JeremyJStarcher/retro-keys/keyboards/c64-vic20/imgs/c64-keyboard-stickers.png

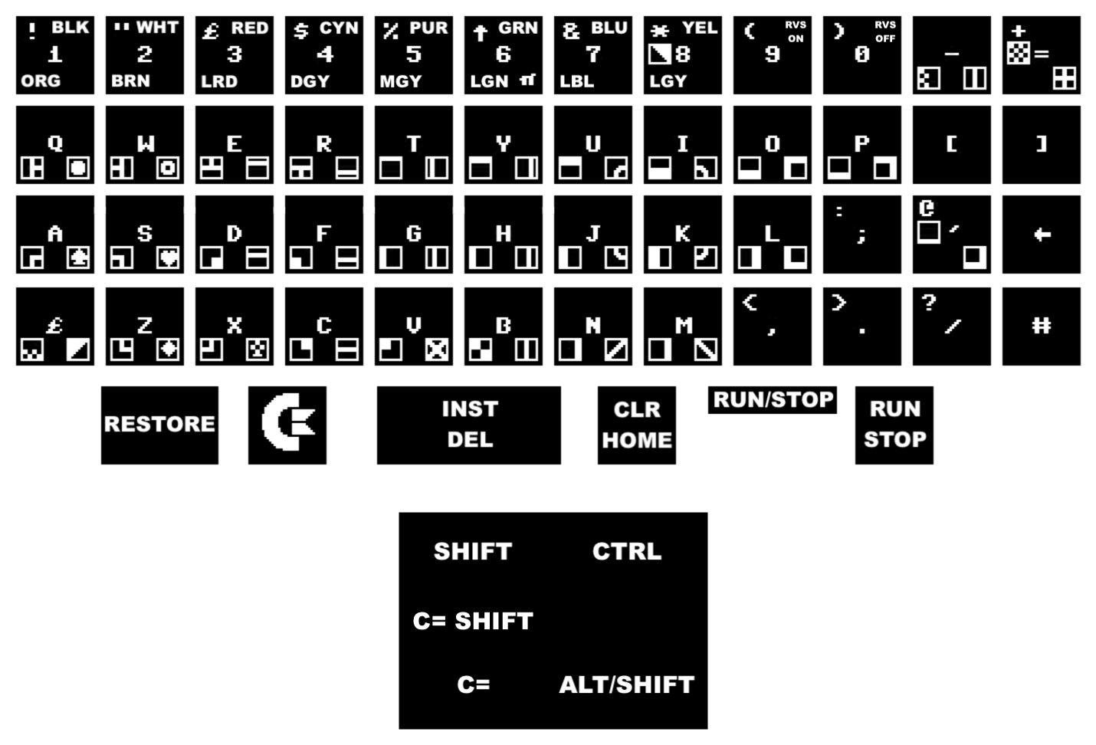
keyboards/c64-vic20/imgs/c64-keyboard-stickers.png
