JeremyJStarcher/retro-keys/keyboards/openscad/puzzlecut/images/OctopusThickLegs.png

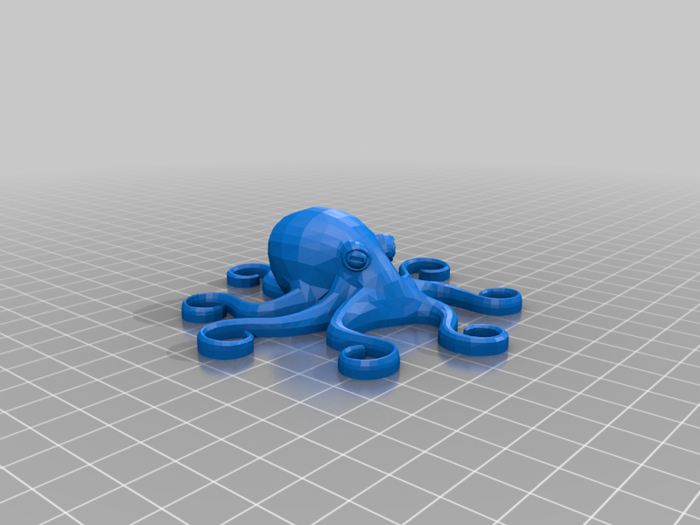
keyboards/openscad/puzzlecut/images/OctopusThickLegs.png
