JeremyJStarcher/retro-keys/keyboards/kicad-lib/3d-models/SOD-diodes/SOD-923 0.3mm Lead Width.step

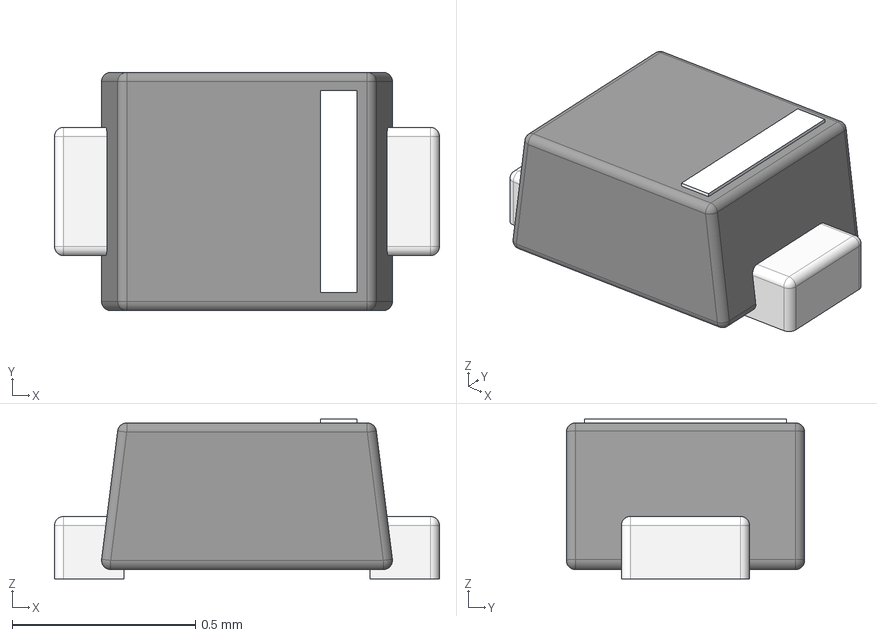
[picture p33: CAD file, 2022-12-26]
keyboards/kicad-lib/3d-models/SOD-diodes/SOD-923 0.3mm Lead Width.step
1.05 x 0.65 x 0.435 mm
