JeremyJStarcher/retro-keys/keyboards/atari-a8/case/case-position.scad

include <../../openscad/utils.scad>;
BASE_THICKNESS = 4;
BOARD_X1 = -216.81315;
BOARD_Y1 = 236.4081;
BOARD_X2 = 138.94315;
BOARD_Y2 = 377.8519;
BOARD_LEN = 355.7563;
BOARD_WIDTH = 141.44379999999998;
CASE_HEIGHT = 10;
STANDOFF_HOLE_INNER_DIAMETER = 4.4;
STANDOFF_HOLE_OUTER_DIAMETER = 6;
STANDOFF_HOLE_HEIGHT = 5;
MOUNTING_HOLE_D = 3.2;
MOUNTING_HOLE_OFFSET = 5;
keyStandoffs = [
[48.935050000000004,-203.38],
[72.7475,-203.38],
[91.7975,-203.38],
[110.8475,-203.38],
[129.8975,-203.38],
[148.9475,-203.38],
[167.9975,-203.38],
[187.0475,-203.38],
[206.0975,-203.38],
[225.1475,-203.38],
[244.1975,-203.38],
[263.2475,-203.38],
[282.2975,-203.38],
[301.3475,-203.38],
[320.3975,-260.53000000000003],
[301.3475,-279.58],
[320.3975,-279.58],
[339.4475,-279.58],
[48.935050000000004,-222.43],
[82.27250000000001,-222.43],
[101.3225,-222.43],
[120.3725,-222.43],
[139.4225,-222.43],
[158.4725,-222.43],
[177.5225,-222.43],
[196.5725,-222.43],
[215.6225,-222.43],
[234.6725,-222.43],
[253.72250000000003,-222.43],
[272.7725,-222.43],
[291.8225,-222.43],
[314.8725,-229.43],
[365.6413,-177.1862],
[365.6413,-205.7612],
[365.6413,-229.5737],
[365.6413,-253.38620000000003],
[48.935,-241.48000000000002],
[87.035,-241.48000000000002],
[106.08500000000001,-241.48000000000002],
[125.13499999999999,-241.48000000000002],
[144.185,-241.48000000000002],
[163.235,-241.48000000000002],
[182.285,-241.48000000000002],
[201.335,-241.48000000000002],
[220.385,-241.48000000000002],
[239.435,-241.48000000000002],
[258.485,-241.48000000000002],
[277.535,-241.48000000000002],
[296.585,-241.48000000000002],
[315.63505,-241.48000000000002],
[365.6413,-277.19870000000003],
[113.2288,-177.1862],
[151.3288,-177.1862],
[175.1413,-177.1862],
[79.89125,-279.58],
[53.69755000000001,-265.53000000000003],
[96.56,-260.53000000000003],
[115.61,-260.53000000000003],
[134.66,-260.53000000000003],
[153.71,-260.53000000000003],
[172.76,-260.53000000000003],
[191.81,-260.53000000000003],
[210.86,-260.53000000000003],
[229.91,-260.53000000000003],
[248.95999999999998,-260.53000000000003],
[268.01,-260.53000000000003],
[287.06005,-260.53000000000003],
[294.2038,-177.1862],
[318.0163,-177.1862],
[139.42255,-279.58],
];
keyBoundingBoxes = [
["ESC", 48.935050000000004, -201.88, 72.74755, -220.92999999999998],
["1", 72.7475, -201.88, 91.7975, -220.92999999999998],
["2", 91.7975, -201.88, 110.8475, -220.92999999999998],
["3", 110.8475, -201.88, 129.8975, -220.92999999999998],
["4", 129.8975, -201.88, 148.94750000000002, -220.92999999999998],
["5", 148.9475, -201.88, 167.9975, -220.92999999999998],
["6", 167.9975, -201.88, 187.0475, -220.92999999999998],
["7", 187.0475, -201.88, 206.09750000000003, -220.92999999999998],
["8", 206.0975, -201.88, 225.1475, -220.92999999999998],
["9", 225.1475, -201.88, 244.19750000000002, -220.92999999999998],
["0", 244.1975, -201.88, 263.2475, -220.92999999999998],
["LT", 263.2475, -201.88, 282.2975, -220.92999999999998],
["GT", 282.2975, -201.88, 301.3475, -220.92999999999998],
["BS", 301.3475, -201.88, 339.4475, -220.92999999999998],
["C_UP", 320.3975, -259.03000000000003, 339.4475, -278.08000000000004],
["C_LEFT", 301.3475, -278.08, 320.39750000000004, -297.13],
["C_DOWN", 320.3975, -278.08, 339.4475, -297.13],
["C_RIGHT", 339.4475, -278.08, 358.4975, -297.13],
["TAB", 48.935050000000004, -220.93, 82.27255, -239.98],
["Q", 82.27250000000001, -220.93, 101.3225, -239.98],
["W", 101.3225, -220.93, 120.3725, -239.98],
["E", 120.3725, -220.93, 139.4225, -239.98],
["R", 139.4225, -220.93, 158.47250000000003, -239.98],
["T", 158.4725, -220.93, 177.5225, -239.98],
["Y", 177.5225, -220.93, 196.57250000000002, -239.98],
["U", 196.5725, -220.93, 215.6225, -239.98],
["I", 215.6225, -220.93, 234.6725, -239.98],
["O", 234.6725, -220.93, 253.72250000000003, -239.98],
["P", 253.72250000000003, -220.93, 272.77250000000004, -239.98],
["DASH", 272.7725, -220.93, 291.8225, -239.98],
["EQUAL", 291.8225, -220.93, 310.8725, -239.98],
["RETURN", 310.8725, -220.93, 339.4475, -239.98],
["HELP", 365.6413, -175.6862, 384.6913, -194.7362],
["RESET", 365.6413, -204.2612, 384.6913, -223.31119999999999],
["OPTION", 365.6413, -228.0737, 384.6913, -247.12369999999999],
["SELECT", 365.6413, -251.88620000000003, 384.6913, -270.93620000000004],
["CONTROL", 48.935, -239.98000000000002, 87.03500000000001, -259.03000000000003],
["A", 87.035, -239.98000000000002, 106.085, -259.03000000000003],
["S", 106.08500000000001, -239.98000000000002, 125.135, -259.03000000000003],
["D", 125.13499999999999, -239.98000000000002, 144.185, -259.03000000000003],
["F", 144.185, -239.98000000000002, 163.235, -259.03000000000003],
["G", 163.235, -239.98000000000002, 182.28500000000003, -259.03000000000003],
["H", 182.285, -239.98000000000002, 201.335, -259.03000000000003],
["J", 201.335, -239.98000000000002, 220.38500000000002, -259.03000000000003],
["K", 220.385, -239.98000000000002, 239.435, -259.03000000000003],
["L", 239.435, -239.98000000000002, 258.485, -259.03000000000003],
["SEMI", 258.485, -239.98000000000002, 277.535, -259.03000000000003],
["PLUS", 277.535, -239.98000000000002, 296.58500000000004, -259.03000000000003],
["ASTRIX", 296.585, -239.98000000000002, 315.635, -259.03000000000003],
["CAPS", 315.63505, -239.98000000000002, 339.44755, -259.03000000000003],
["START", 365.6413, -275.69870000000003, 384.6913, -294.74870000000004],
["POWER", 113.2288, -175.6862, 132.27880000000002, -194.7362],
["MENU", 151.3288, -175.6862, 170.3788, -194.7362],
["TURBO", 175.1413, -175.6862, 194.1913, -194.7362],
["FN", 79.89125, -278.08, 113.22874999999999, -297.13],
["LSHIFT", 53.69755000000001, -259.03000000000003, 96.56005, -278.08000000000004],
["Z", 96.56, -259.03000000000003, 115.61, -278.08000000000004],
["X", 115.61, -259.03000000000003, 134.66, -278.08000000000004],
["C", 134.66, -259.03000000000003, 153.71, -278.08000000000004],
["V", 153.71, -259.03000000000003, 172.76000000000002, -278.08000000000004],
["B", 172.76, -259.03000000000003, 191.81, -278.08000000000004],
["N", 191.81, -259.03000000000003, 210.86, -278.08000000000004],
["M", 210.86, -259.03000000000003, 229.91000000000003, -278.08000000000004],
["COMMA", 229.91, -259.03000000000003, 248.96, -278.08000000000004],
["PERIOD", 248.95999999999998, -259.03000000000003, 268.01, -278.08000000000004],
["SLASH", 268.01, -259.03000000000003, 287.06, -278.08000000000004],
["RSHIFT", 287.06005, -259.03000000000003, 320.39755, -278.08000000000004],
["INV", 294.2038, -175.6862, 313.2538, -194.7362],
["BREAK", 318.0163, -175.6862, 337.0663, -194.7362],
["SPACE", 139.42255, -278.08, 258.48505, -297.13],
];

CASE_PIECES = 4;
CASE_PIECE = 1;


main(BOARD_WIDTH, BOARD_LEN, CASE_PIECES, CASE_PIECE);
